Syka2210/Laguna3Navigation/3D parts/Parts/Fan_30x30x8_5V_2pin.stp

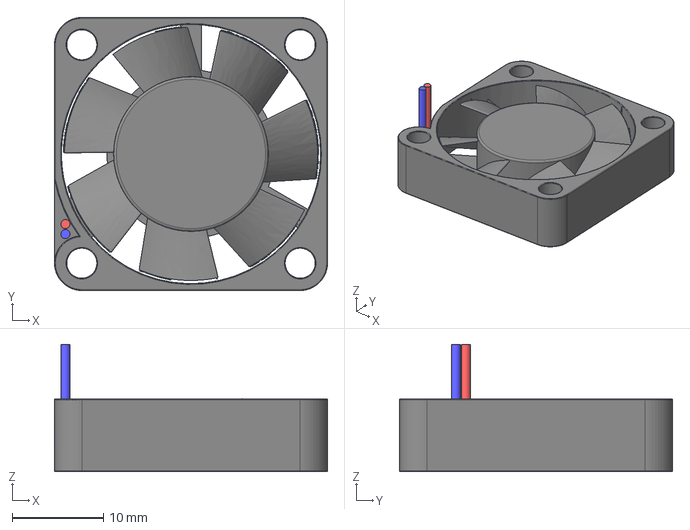
[picture p13: CAD file, 2022-10-02]
3D parts/Parts/Fan_30x30x8_5V_2pin.stp
30.0 x 30.0 x 14.0 mm
Rotator
