Syka2210/Laguna3Navigation/3D parts/STL files/Latch V3.STL

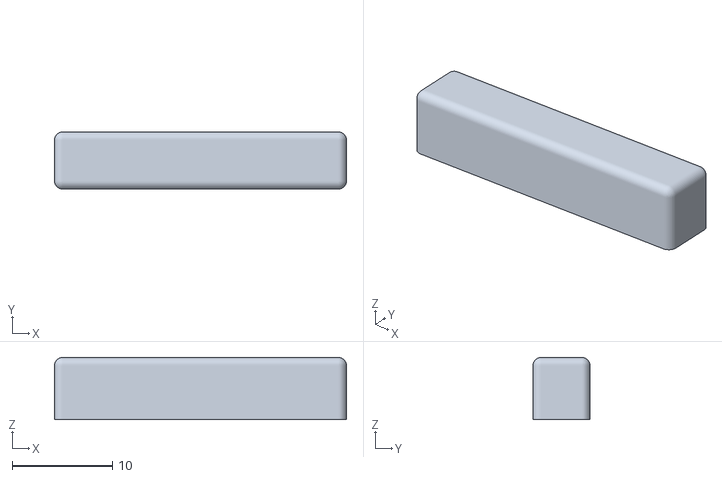
[picture p18: CAD file, 2022-05-14]
3D parts/STL files/Latch V3.STL
29.2 x 5.70 x 6.20
