Syka2210/Laguna3Navigation/3D parts/Parts/XH2.54 3p.SLDPRT

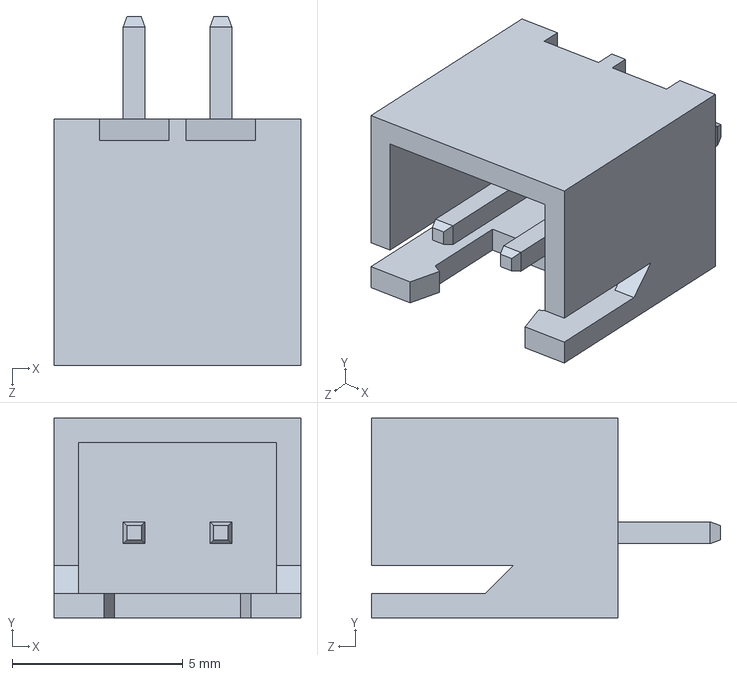
[picture p19: CAD file, 2022-05-14]
3D parts/Parts/XH2.54 3p.SLDPRT
7.21 x 5.84 x 10.2 mm
