Syka2210/Laguna3Navigation/3D parts/STL files/display case v3 - left.STL

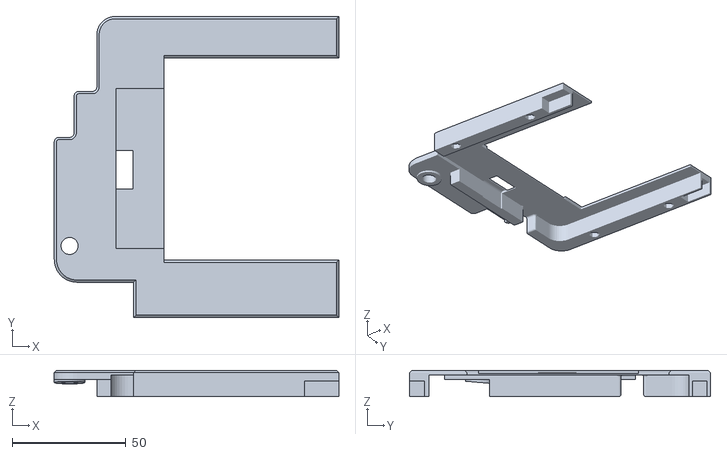
[picture p20: CAD file, 2022-05-14]
3D parts/STL files/display case v3 - left.STL
125.2 x 132.5 x 11.6
