Syka2210/Laguna3Navigation/3D parts/Carcasa Navigatie V4.0/PCB.SLDPRT

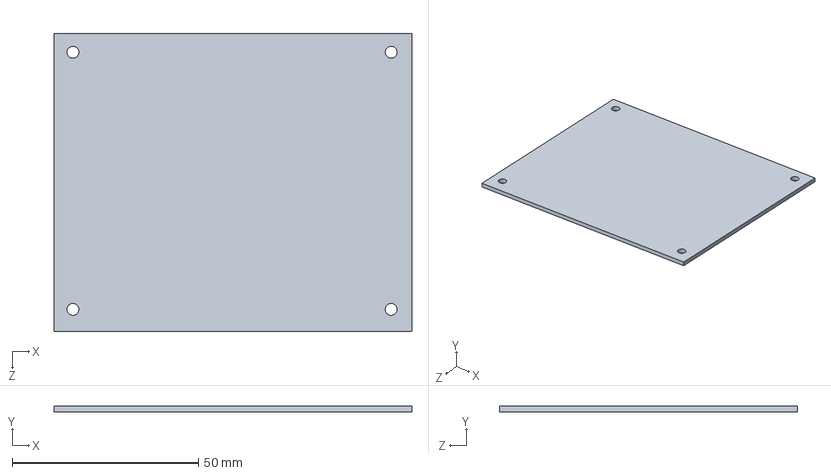
[picture p21: CAD file, 2022-05-14]
3D parts/Carcasa Navigatie V4.0/PCB.SLDPRT
96.0 x 1.60 x 80.0 mm
