Syka2210/Laguna3Navigation/3D parts/Parts/JST - XH - Thru (V) - 4Pin - 2.54mm.SLDPRT

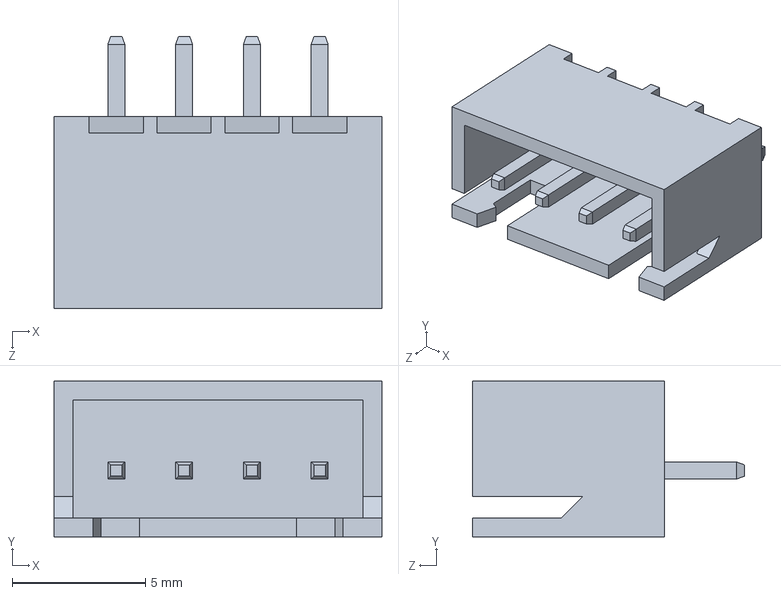
[picture p22: CAD file, 2022-05-14]
3D parts/Parts/JST - XH - Thru (V) - 4Pin - 2.54mm.SLDPRT
12.3 x 5.84 x 10.2 mm
