Syka2210/Laguna3Navigation/3D parts/STL files/display case v3 - right.STL

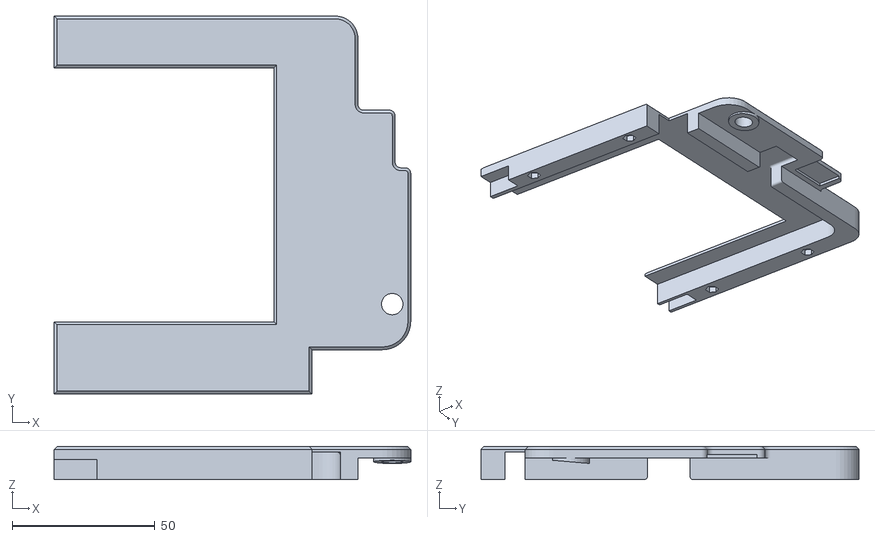
[picture p23: CAD file, 2022-05-14]
3D parts/STL files/display case v3 - right.STL
125.0 x 132.5 x 11.6
