Syka2210/Laguna3Navigation/3D parts/Carcasa Navigatie V4.0/Nexus7_2013 V1.2.SLDPRT

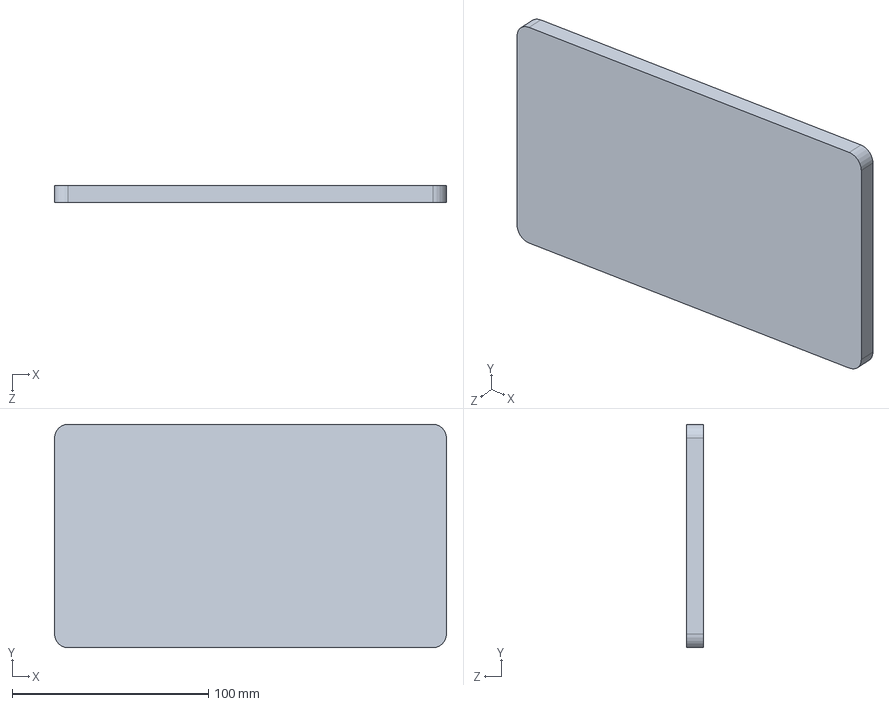
[picture p24: CAD file, 2022-05-14]
3D parts/Carcasa Navigatie V4.0/Nexus7_2013 V1.2.SLDPRT
200.0 x 114.0 x 8.70 mm
