Syka2210/Laguna3Navigation/3D parts/STL files/Cable ring connector.STL

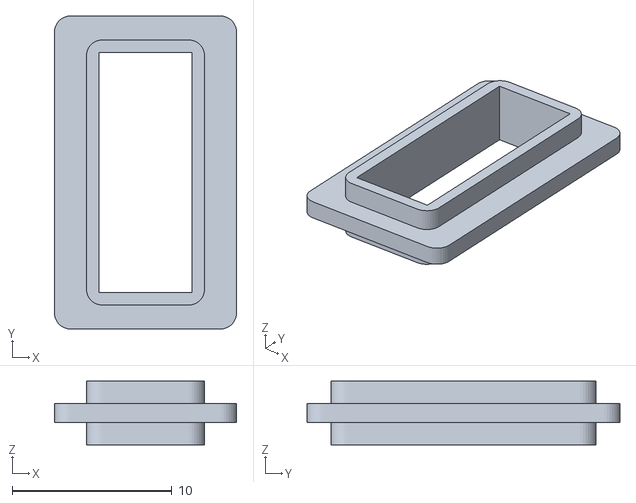
[picture p25: CAD file, 2022-05-14]
3D parts/STL files/Cable ring connector.STL
11.4 x 19.6 x 4.00
