Syka2210/Laguna3Navigation/3D parts/Carcasa Navigatie V4.0/display case v3.0.STL

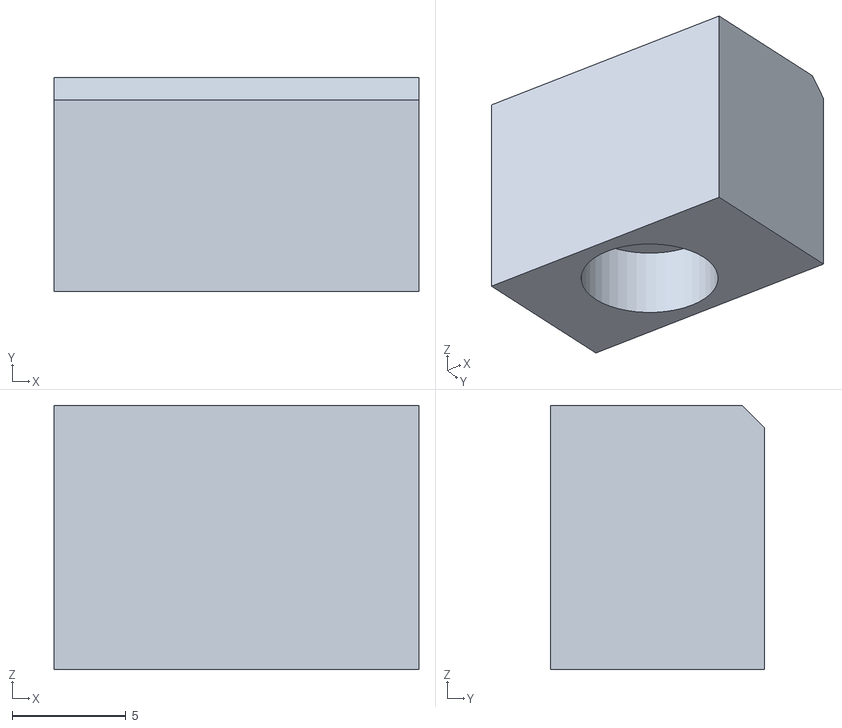
[picture p26: CAD file, 2022-05-14]
3D parts/Carcasa Navigatie V4.0/display case v3.0.STL
16.0 x 9.40 x 11.6
