Syka2210/Laguna3Navigation/3D parts/STL files/Cable ring.STL

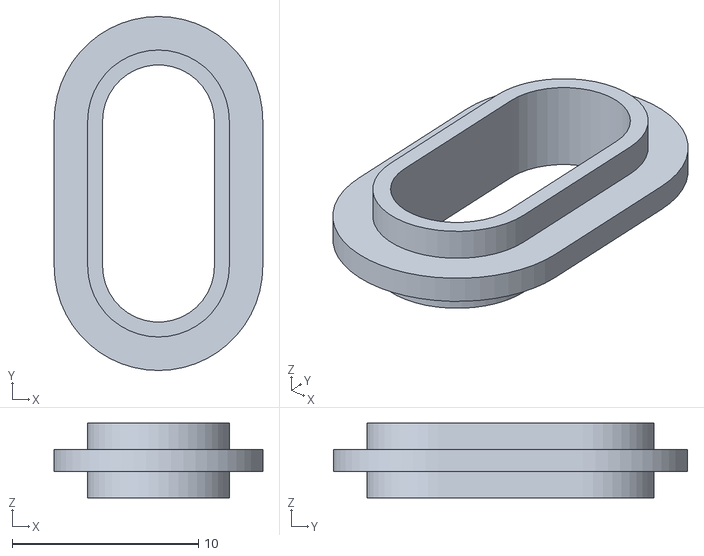
[picture p27: CAD file, 2022-05-14]
3D parts/STL files/Cable ring.STL
11.2 x 19.0 x 4.00
