Syka2210/Laguna3Navigation/3D parts/STL files/PCB case v3.0 - upper.STL

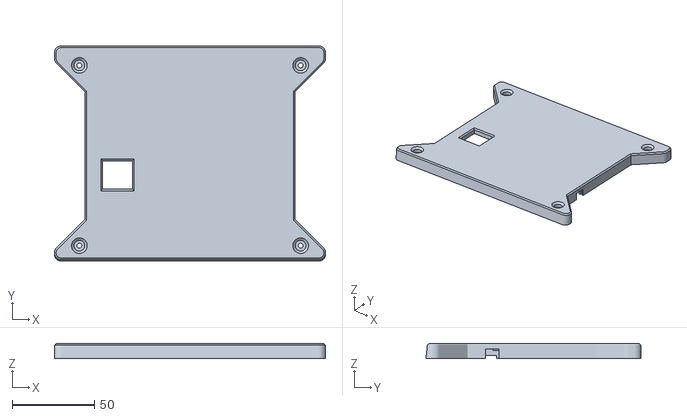
[picture p28: CAD file, 2022-05-14]
3D parts/STL files/PCB case v3.0 - upper.STL
164.9 x 130.9 x 9.00
