Syka2210/Laguna3Navigation/3D parts/Carcasa Navigatie V4.0/Back_cover(display case).sldprt

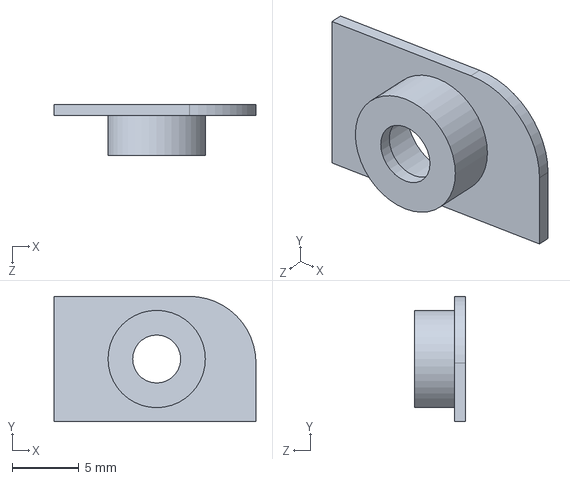
[picture p29: CAD file, 2022-05-14]
3D parts/Carcasa Navigatie V4.0/Back_cover(display case).sldprt
15.2 x 9.40 x 3.80 mm
