Syka2210/Laguna3Navigation/3D parts/STL files/front clips.STL

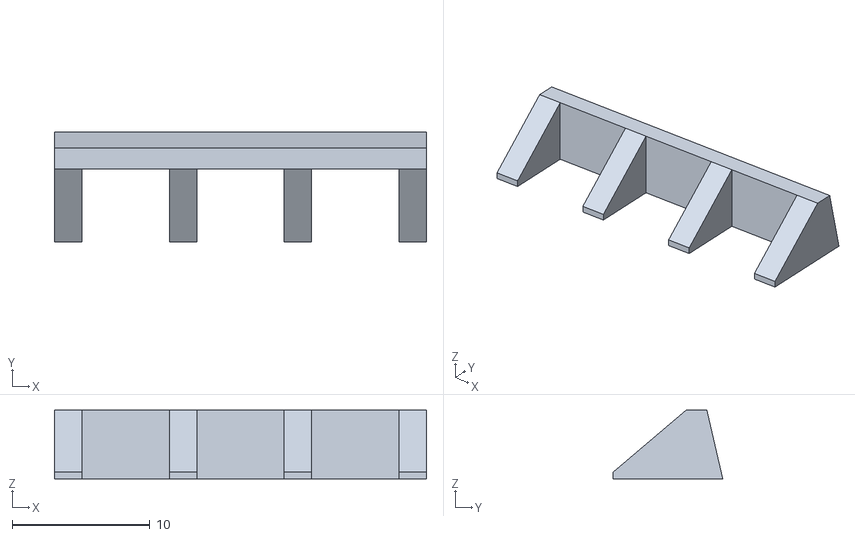
[picture p30: CAD file, 2022-05-14]
3D parts/STL files/front clips.STL
27.0 x 7.95 x 5.00
