Syka2210/Laguna3Navigation/3D parts/Carcasa Navigatie V4.0/rj45.SLDPRT

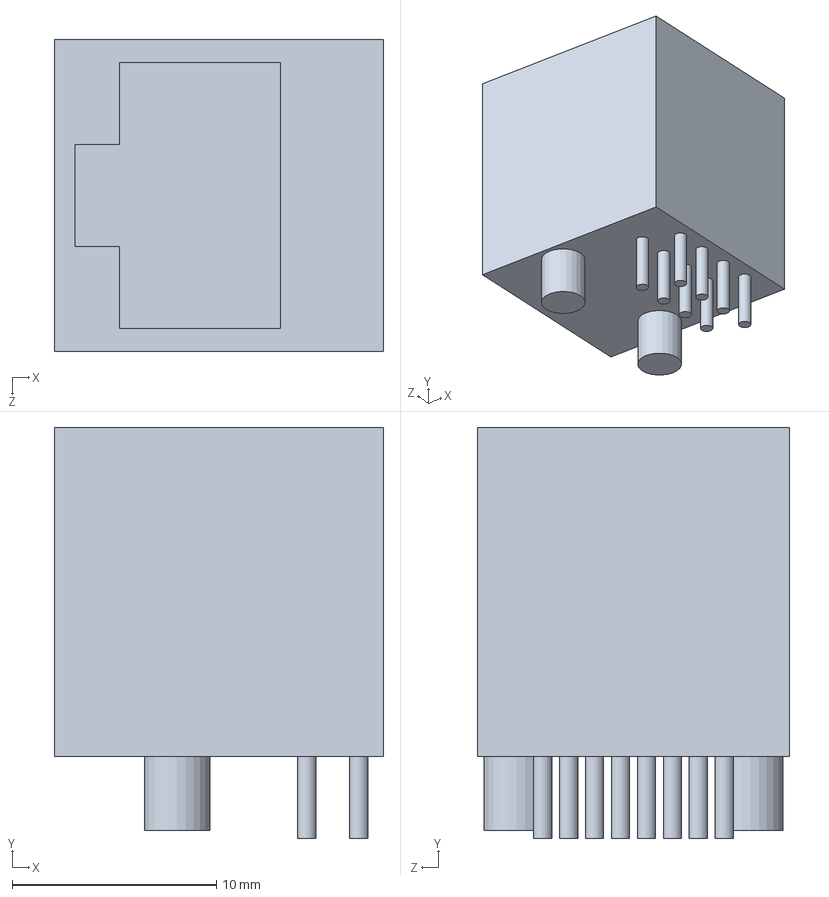
[picture p31: CAD file, 2022-05-14]
3D parts/Carcasa Navigatie V4.0/rj45.SLDPRT
16.1 x 20.1 x 15.2 mm
