Syka2210/Laguna3Navigation/3D parts/Carcasa Navigatie V4.0/Cable ring connector - 4 pins.SLDPRT

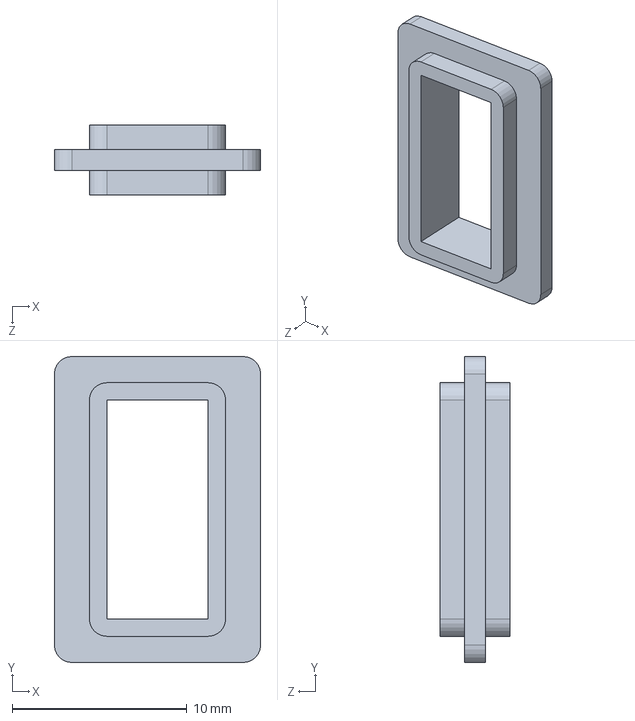
[picture p32: CAD file, 2022-05-14]
3D parts/Carcasa Navigatie V4.0/Cable ring connector - 4 pins.SLDPRT
11.8 x 17.5 x 4.00 mm
